dukelec/cdbus/hdl/cd_tx_bytes.v

/*
 * This Source Code Form is subject to the terms of the CERN Open
 * Hardware Licence Version 2 - Strongly Reciprocal (CERN-OHL-S v2):
 * https://ohwr.org/cern_ohl_s_v2.txt (see the LICENSE file).
 * Notice: The CDBUS Exception (see the LICENSE_EXCEPTION file)
 * grants free commercial use in FPGAs and other programmable logic
 * devices; it does not extend to ASIC design or manufacturing.
 *
 * Copyright (c) 2017-2026 DUKELEC, All rights reserved.
 *
 * Author: Duke Fong <d@d-l.io>
 */

module cd_tx_bytes(
        input               clk,
        input               reset_n,

        input               user_crc,
        input               raw,        // transparent mode: skip the first 3 bytes
        input               abort,

        output reg  [7:0]   data,
        output              has_data,
        input               ack_data,
        output reg          is_crc_byte,
        output reg          is_last_byte,
        input       [15:0]  crc_data,

        input               ram_unread,
        input               ram_wr_en,
        input       [7:0]   ram_rd_byte,
        output      [7:0]   ram_rd_addr,
        output              ram_rd_en,
        output reg          ram_rd_done
    );

assign has_data = ram_unread && !ram_rd_done && hdr_done;
assign ram_rd_en = ram_unread;

reg [8:0] byte_cnt;
assign ram_rd_addr = byte_cnt[7:0];
reg [7:0] data_len; // backup 3rd byte
reg hdr_done;       // raw mode: header prefetched, 2 clocks per byte for ram latency
reg pf_tick;


always @(posedge clk)
    if (!ram_unread || ram_rd_done) begin
        byte_cnt <= 0;
        data_len <= 0;
        hdr_done <= !raw;
        pf_tick <= 0;
        is_crc_byte <= 0;
        is_last_byte <= 0;
    end
    else begin
        data <= ram_rd_byte;
        pf_tick <= !pf_tick && !ram_wr_en; // read lost to write in single port ram

        if (byte_cnt == 2) begin
            data_len <= ram_rd_byte;
            if (pf_tick)
                hdr_done <= 1;
        end

        // we have enough time to change the byte which send at second bit
        else if (byte_cnt == data_len + 3) begin
            if (!user_crc)
                data <= crc_data[7:0];
            is_crc_byte <= 1;
        end
        else if (byte_cnt == data_len + 4) begin
            if (!user_crc)
                data <= crc_data[15:8];
            is_last_byte <= 1;
        end

        if (ack_data || (pf_tick && !hdr_done))
            byte_cnt <= byte_cnt + 1'd1;
    end


always @(posedge clk) begin
    ram_rd_done <= 0;
    if (abort || (is_last_byte && ack_data))
        ram_rd_done <= 1;
end

endmodule
