dukelec/cdbus/tests/cdbus_wrapper_dft.v

/*
 * This Source Code Form is subject to the terms of the CERN Open
 * Hardware Licence Version 2 - Strongly Reciprocal (CERN-OHL-S v2):
 * https://ohwr.org/cern_ohl_s_v2.txt (see the LICENSE file).
 * Notice: The CDBUS Exception (see the LICENSE_EXCEPTION file)
 * grants free commercial use in FPGAs and other programmable logic
 * devices; it does not extend to ASIC design or manufacturing.
 *
 * Copyright (c) 2017-2026 DUKELEC, All rights reserved.
 *
 * Author: Duke Fong <d@d-l.io>
 */

`timescale 1 ns / 1 ps
`define CD_CHIP_SELECT

module cdbus_wrapper_dft(
        input       clk0,
        input       clk1,
        input       clk2,
        input       reset0,
        input       reset1,
        input       reset2,
        input       cs0,
        input       cs1,
        input       cs2,

        input       [4:0] csr_addr0,
        input       csr_read0,
        output      [7:0] csr_rdata0,
        input       csr_write0,
        input       [7:0] csr_wdata0,

        input       [4:0] csr_addr1,
        input       csr_read1,
        output      [7:0] csr_rdata1,
        input       csr_write1,
        input       [7:0] csr_wdata1,

        input       [4:0] csr_addr2,
        input       csr_read2,
        output      [7:0] csr_rdata2,
        input       csr_write2,
        input       [7:0] csr_wdata2,

        output      irq0,
        output      irq1,
        output      irq2,

        inout       bus_a,

        input       dbg0,
        input       dbg1
    );

wire tx0;
wire tx1;
wire tx2;
wire tx_en0;
wire tx_en1;
wire tx_en2;

wire rx0 = tx_en0 === 1 ? tx0 : (bus_a === 1'bx ? 1'bx : (bus_a !== 0));
wire rx1 = tx_en1 === 1 ? tx1 : (bus_a === 1'bx ? 1'bx : (bus_a !== 0));
wire rx2 = tx_en2 === 1 ? tx2 : (bus_a === 1'bx ? 1'bx : (bus_a !== 0));

wire b0_is0 = tx_en0 === 1 && tx0 === 0;
wire b1_is0 = tx_en1 === 1 && tx1 === 0;
wire b2_is0 = tx_en2 === 1 && tx2 === 0;
wire b0_is1 = tx_en0 === 1 && tx0 === 1;
wire b1_is1 = tx_en1 === 1 && tx1 === 1;
wire b2_is1 = tx_en2 === 1 && tx2 === 1;

wire [2:0] is0_cnt = b0_is0 + b1_is0 + b2_is0;
wire [2:0] is1_cnt = b0_is1 + b1_is1 + b2_is1;

reg bus_reg;
assign bus_a = bus_reg;

always @(*)
    if (is0_cnt == 0 && is1_cnt != 0)
        bus_reg = 1;
    else if (is0_cnt != 0 && is1_cnt == 0)
        bus_reg = 0;
    else if (is0_cnt == 0 && is1_cnt == 0)
        bus_reg = 1'bz;
    else
        bus_reg = 1'bx;


cdbus cdbus_m0(
          .clk(clk0),
          .reset_n(reset0),
          .chip_select(cs0),
          .irq(irq0),
          
          .csr_address(csr_addr0),
          .csr_read(csr_read0),
          .csr_readdata(csr_rdata0),
          .csr_write(csr_write0),
          .csr_writedata(csr_wdata0),
          
          .rx(rx0),
          .tx(tx0),
          .tx_en(tx_en0)
      );

cdbus cdbus_m1(
          .clk(clk1),
          .reset_n(reset1),
          .chip_select(cs1),
          .irq(irq1),
          
          .csr_address(csr_addr1),
          .csr_read(csr_read1),
          .csr_readdata(csr_rdata1),
          .csr_write(csr_write1),
          .csr_writedata(csr_wdata1),
          
          .rx(rx1),
          .tx(tx1),
          .tx_en(tx_en1)
      );

cdbus cdbus_m2(
          .clk(clk2),
          .reset_n(reset2),
          .chip_select(cs2),
          .irq(irq2),
          
          .csr_address(csr_addr2),
          .csr_read(csr_read2),
          .csr_readdata(csr_rdata2),
          .csr_write(csr_write2),
          .csr_writedata(csr_wdata2),
          
          .rx(rx2),
          .tx(tx2),
          .tx_en(tx_en2)
      );

initial begin
    $dumpfile("cdbus.vcd");
    $dumpvars();
end

endmodule
