dukelec/cdbus/tests/common.py

# This Source Code Form is subject to the terms of the CERN Open
# Hardware Licence Version 2 - Strongly Reciprocal (CERN-OHL-S v2):
# https://ohwr.org/cern_ohl_s_v2.txt (see the LICENSE file).
# Notice: The CDBUS Exception (see the LICENSE_EXCEPTION file)
# grants free commercial use in FPGAs and other programmable logic
# devices; it does not extend to ASIC design or manufacturing.
#
# Copyright (c) 2017-2026 DUKELEC, All rights reserved.
#
# Author: Duke Fong <d@d-l.io>
#

import cocotb
from cocotb.types import Logic, LogicArray
from cocotb.triggers import RisingEdge, FallingEdge, ReadOnly, Timer
from cocotb.clock import Clock

# pip3 install pythoncrc
from PyCRC.CRC16 import CRC16

def modbus_crc(data):
    return CRC16(modbus_flag=True).calculate(data).to_bytes(2, byteorder='little')

IS_32BITS           = False
DFT_VERSION         = 0x0f

REG_VERSION         = 0x00
REG_SETTING         = 0x02
REG_PIN_CFG         = 0x03
REG_IDLE_WAIT_LEN   = 0x04
REG_TX_PERMIT_LEN_L = 0x05
REG_TX_PERMIT_LEN_H = 0x06
REG_MAX_IDLE_LEN_L  = 0x07
REG_MAX_IDLE_LEN_H  = 0x08
REG_TX_PRE_LEN      = 0x09
REG_FILTER          = 0x0b
REG_DIV_LS_L        = 0x0c
REG_DIV_LS_H        = 0x0d
REG_DIV_HS_L        = 0x0e
REG_DIV_HS_H        = 0x0f
REG_INT_MASK_L      = 0x10
REG_INT_MASK_H      = 0x11
REG_INT_FLAG_L      = 0x12
REG_INT_FLAG_H      = 0x13
REG_RX_LEN          = 0x14
REG_DAT             = 0x15
REG_CTRL            = 0x16
REG_DAT_HOLD        = 0x17
REG_RX_ADDR         = 0x18
REG_FILTER_M0       = 0x1a
REG_FILTER_M1       = 0x1b
REG_FILTER_MSK0     = 0x1c
REG_FILTER_MSK1     = 0x1d

BIT_SETTING_NO_DROP         = 1 << 5
BIT_SETTING_USER_CRC        = 1 << 4
BIT_SETTING_RAW_LOOPBACK    = 1 << 3
BIT_SETTING_RAW             = 1 << 2
BIT_SETTING_MODE_HALF       = 0 << 0
BIT_SETTING_MODE_ARBIT      = 1 << 0
BIT_SETTING_MODE_BS         = 2 << 0
BIT_SETTING_MODE_FULL       = 3 << 0

BIT_PIN_CFG_RX_INVERT       = 1 << 3
BIT_PIN_CFG_TX_INVERT       = 1 << 2
BIT_PIN_CFG_TX_KEEP_LOW     = 1 << 1
BIT_PIN_CFG_TX_PUSH_PULL    = 1 << 0

BIT_FLAG_TX_ERROR           = 1 << 7
BIT_FLAG_TX_CD              = 1 << 6
BIT_FLAG_TX_BUF_CLEAN       = 1 << 5
BIT_FLAG_TX_BUF_FREE        = 1 << 4
BIT_FLAG_RX_ERROR           = 1 << 3
BIT_FLAG_RX_LOST            = 1 << 2
BIT_FLAG_RX_BREAK           = 1 << 1
BIT_FLAG_RX_PENDING         = 1 << 0

BIT_RX_RST                  = 1 << 7
BIT_RX_CLR_PENDING          = 1 << 4
BIT_TX_ABORT                = 1 << 3
BIT_TX_DROP                 = 1 << 2
BIT_TX_SEND_BREAK           = 1 << 1
BIT_TX_START                = 1 << 0


async def _send_bytes(dut, bytes_, sys_clk, factor, is_z=True):
    clk_period = 1000000000000 / sys_clk
    await Timer(1000)
    factor += 1
    for byte in bytes_:
        dut.bus_a.value = 0
        await Timer(factor * clk_period)
        for i in range(0, 8):
            if byte & 0x01 == 0:
                dut.bus_a.value = 0
            else:
                dut.bus_a.value = Logic('z') if is_z else 1
            await Timer(factor * clk_period)
            byte = byte >> 1
        dut.bus_a.value = Logic('z') if is_z else 1
        await Timer(factor * clk_period)
        dut.bus_a.value = Logic('z')

# Pass in a frame of data from the outside of the dut.
async def send_frame(dut, bytes_, sys_clk, factor_l, factor_h):
    await _send_bytes(dut, bytes_[0:1], sys_clk, factor_l)
    await _send_bytes(dut, bytes_[1:], sys_clk, factor_h, False)
    await _send_bytes(dut, modbus_crc(bytes_), sys_clk, factor_h, False)


async def reset(dut, idx, duration=10000):
    dut._log.debug(f'idx{idx}: resetting')
    getattr(dut, f'reset{idx}').value = 0
    await Timer(duration)
    await RisingEdge(getattr(dut, f'clk{idx}'))
    getattr(dut, f'reset{idx}').value = 1
    dut._log.debug(f'idx{idx}: out of reset')
    getattr(dut, f'cs{idx}').value = 0

# the read is taken at the clock edge, the data is valid in the clock after it
# (csr_address is kept until then); a burst takes one byte per clock
async def csr_read(dut, idx, address, len_=1):
    await RisingEdge(getattr(dut, f'clk{idx}'))
    getattr(dut, f'cs{idx}').value = 1
    getattr(dut, f'csr_addr{idx}').value = address
    getattr(dut, f'csr_read{idx}').value = 1
    ret = []
    for i in range(len_):
        await RisingEdge(getattr(dut, f'clk{idx}'))
        if i == len_ - 1:
            getattr(dut, f'csr_read{idx}').value = 0
            getattr(dut, f'cs{idx}').value = 0
        await ReadOnly()
        ret.append(getattr(dut, f'csr_rdata{idx}').value)
    await RisingEdge(getattr(dut, f'clk{idx}')) # leave the read-only phase
    return ret if len_ > 1 else ret[0]

async def csr_write(dut, idx, address, data, burst=False):
    addr_len = len(getattr(dut, f'csr_addr{idx}'))
    wdata_len = len(getattr(dut, f'csr_wdata{idx}'))
    
    await RisingEdge(getattr(dut, f'clk{idx}'))
    getattr(dut, f'cs{idx}').value = 1
    getattr(dut, f'csr_addr{idx}').value = address
    getattr(dut, f'csr_wdata{idx}').value = data
    getattr(dut, f'csr_write{idx}').value = 1
    if not burst:
        await RisingEdge(getattr(dut, f'clk{idx}'))
        getattr(dut, f'csr_write{idx}').value = 0
        getattr(dut, f'csr_addr{idx}').value = LogicArray('x' * addr_len)
        getattr(dut, f'csr_wdata{idx}').value = LogicArray('x' * wdata_len)
        getattr(dut, f'cs{idx}').value = 0


async def check_version(dut, idx):
    value = await csr_read(dut, idx, REG_VERSION)
    dut._log.info(f'idx{idx}: REG_VERSION: 0x%02x' % int(value))
    if value != DFT_VERSION:
        dut._log.error(f'idx{idx}: version mismatch')
        exit(-1)

async def set_div(dut, idx, div_ls, div_hs):
    await csr_write(dut, idx, REG_DIV_LS_H, div_ls >> 8, True)
    await csr_write(dut, idx, REG_DIV_LS_L, div_ls & 0xff, True)
    await csr_write(dut, idx, REG_DIV_HS_H, div_hs >> 8, True)
    await csr_write(dut, idx, REG_DIV_HS_L, div_hs & 0xff, False)

async def set_max_idle_len(dut, idx, max_idle_len):
    await csr_write(dut, idx, REG_MAX_IDLE_LEN_H, max_idle_len >> 8, True)
    await csr_write(dut, idx, REG_MAX_IDLE_LEN_L, max_idle_len & 0xff, False)

async def set_tx_permit_len(dut, idx, tx_permit_len):
    await csr_write(dut, idx, REG_TX_PERMIT_LEN_H, tx_permit_len >> 8, True)
    await csr_write(dut, idx, REG_TX_PERMIT_LEN_L, tx_permit_len & 0xff, False)

async def write_tx(dut, idx, bytes_, reg=REG_DAT):
    if len(bytes_) == 0:
        return
    for i in range(len(bytes_)):
        await csr_write(dut, idx, reg, bytes_[i], i < len(bytes_) - 1)
    await RisingEdge(getattr(dut, f'clk{idx}')) # let the auto submit finish before the next transfer

async def seek_rx(dut, idx, offset): # byte offset
    await csr_write(dut, idx, REG_RX_ADDR, offset)

async def read_rx(dut, idx, len_, reg=REG_DAT):
    if len_ == 0:
        return b''
    vals = await csr_read(dut, idx, reg, len_)
    return bytes([int(v) for v in (vals if len_ > 1 else [vals])])

async def read_rx_len(dut, idx):
    return await csr_read(dut, idx, REG_RX_LEN)

async def read_int_flag(dut, idx):
    return await csr_read(dut, idx, REG_INT_FLAG_L)

async def read_int_flag3(dut, idx):
    return await csr_read(dut, idx, REG_INT_FLAG_L, 3)


async def exit_err():
    await Timer(1000, unit='ns')
    exit(-1)

async def exit_ok():
    await Timer(10, unit='us')
    with open('.exit_ok', 'w') as f:
        f.write('ok')
