dukelec/cdbus/tests/test_bs_mode.py

# This Source Code Form is subject to the terms of the CERN Open
# Hardware Licence Version 2 - Strongly Reciprocal (CERN-OHL-S v2):
# https://ohwr.org/cern_ohl_s_v2.txt (see the LICENSE file).
# Notice: The CDBUS Exception (see the LICENSE_EXCEPTION file)
# grants free commercial use in FPGAs and other programmable logic
# devices; it does not extend to ASIC design or manufacturing.
#
# Copyright (c) 2017-2026 DUKELEC, All rights reserved.
#
# Author: Duke Fong <d@d-l.io>
#

from common import *

@cocotb.test(timeout_time=500, timeout_unit='us')
async def test_cdbus(dut):
    dut._log.info('test_cdbus start.')
    
    sys_clk = 40000000
    clk_period = 1000000000000 / sys_clk

    cocotb.start_soon(Clock(dut.clk0, clk_period).start())
    cocotb.start_soon(Clock(dut.clk1, clk_period).start())
    cocotb.start_soon(Clock(dut.clk2, clk_period).start())
    await reset(dut, 0)
    await reset(dut, 1)
    await reset(dut, 2)
    await check_version(dut, 0)
    await check_version(dut, 1)
    await check_version(dut, 2)
    
    val = await csr_read(dut, 0, REG_SETTING)
    dut._log.info(f'idx0 REG_SETTING: 0x{int(val):02x}')

    await csr_write(dut, 0, REG_SETTING, 0b00000010) # bs mode
    await csr_write(dut, 1, REG_SETTING, 0b00000010)
    await csr_write(dut, 2, REG_SETTING, 0b00000010)
    await csr_write(dut, 0, REG_PIN_CFG, 0b00000001) # push-pull
    await csr_write(dut, 1, REG_PIN_CFG, 0b00000001)
    await csr_write(dut, 2, REG_PIN_CFG, 0b00000001)
    await csr_write(dut, 2, REG_INT_MASK_L, 0b11001101) # not select break rx
    
    await set_max_idle_len(dut, 0, 40)
    await set_max_idle_len(dut, 1, 40)
    await set_max_idle_len(dut, 2, 40)
    
    await set_tx_permit_len(dut, 0, 10)
    await set_tx_permit_len(dut, 1, 20)
    await set_tx_permit_len(dut, 2, 30)

    await set_div(dut, 0, 2, 2) # max speed
    await set_div(dut, 1, 2, 2)
    await set_div(dut, 2, 2, 2)
    
    await csr_write(dut, 0, REG_FILTER, 0x55)
    await csr_write(dut, 1, REG_FILTER, 0xa5)
    await csr_write(dut, 2, REG_FILTER, 0x03)
    
    
    await Timer(10, unit='us') # wait exceed max idle
    
    # start tx at same time
    cocotb.start_soon(write_tx(dut, 0, b'\x55\x03\x01\xc5')) # node 0x55 send to 0x03
    cocotb.start_soon(write_tx(dut, 1, b'\xa5\x03\x01\xca')) # node 0xa5 send to 0x03

    await RisingEdge(dut.irq2)
    val = await read_int_flag(dut, 2)
    dut._log.info(f'REG_INT_FLAG: 0x{int(val):02x}')
    if not (int(val) & BIT_FLAG_RX_BREAK):
        dut._log.error(f'idx2: not receive break')
        await exit_err()
    
    str_ = (await read_rx(dut, 2, 4)).hex() # read 4 bytes
    dut._log.info(f'idx2: received: {str_}')
    if str_ != '550301c5':
        dut._log.error(f'idx2: receive mismatch first frame')
        await exit_err()
    
    #await csr_write(dut, 2, REG_CTRL, BIT_RX_CLR_PENDING)
    await Timer(500, unit='ns')
    
    await RisingEdge(dut.irq2)
    val = await read_int_flag(dut, 2)
    dut._log.info(f'REG_INT_FLAG: 0x{int(val):02x}')
    
    str_ = (await read_rx(dut, 2, 4)).hex() # read 4 bytes
    dut._log.info(f'idx2: received: {str_}')
    if str_ != 'a50301ca':
        dut._log.error(f'idx2: receive mismatch second frame')
        await exit_err()
    
    #await csr_write(dut, 2, REG_CTRL, BIT_RX_CLR_PENDING)
    await FallingEdge(dut.irq2)
    
    
    await Timer(10, unit='us') # wait exceed max idle
    
    cocotb.start_soon(write_tx(dut, 1, b'\xa5\x03\x01\xca')) # node 0xa5 send to 0x03
    dut.dbg0.value = 0
    await Timer(2700, unit='ns') # wait frame pending after tx permit
    dut.dbg0.value = 1
    cocotb.start_soon(write_tx(dut, 0, b'\x55\x03\x01\xc5')) # node 0x55 send to 0x03
    
    await RisingEdge(dut.irq2)
    val = await read_int_flag(dut, 2)
    dut._log.info(f'REG_INT_FLAG: 0x{int(val):02x}')
    if not (int(val) & BIT_FLAG_RX_BREAK):
        dut._log.error(f'idx2: not receive break')
        await exit_err()
    
    str_ = (await read_rx(dut, 2, 4)).hex() # read 4 bytes
    dut._log.info(f'idx2: received: {str_}')
    if str_ != 'a50301ca':
        dut._log.error(f'idx2: receive mismatch first frame')
        await exit_err()
    
    #await csr_write(dut, 2, REG_CTRL, BIT_RX_CLR_PENDING)
    await Timer(500, unit='ns')
    
    await RisingEdge(dut.irq2)
    val = await read_int_flag(dut, 2)
    dut._log.info(f'REG_INT_FLAG: 0x{int(val):02x}')
    
    str_ = (await read_rx(dut, 2, 4)).hex() # read 4 bytes
    dut._log.info(f'idx2: received: {str_}')
    if str_ != '550301c5':
        dut._log.error(f'idx2: receive mismatch second frame')
        await exit_err()
    
    #await csr_write(dut, 2, REG_CTRL, BIT_RX_CLR_PENDING)
    await FallingEdge(dut.irq2)
    
    dut._log.info('test_cdbus done.')
    await exit_ok()
