dukelec/cdbus/example/pll/cdctl_pll.v

module cdctl_pll(REFERENCECLK,
                 PLLOUTCORE,
                 PLLOUTGLOBAL,
                 RESET,
                 LOCK);

input REFERENCECLK;
input RESET;    /* To initialize the simulation properly, the RESET signal (Active Low) must be asserted at the beginning of the simulation */ 
output PLLOUTCORE;
output PLLOUTGLOBAL;
output LOCK;

SB_PLL40_CORE cdctl_pll_inst(.REFERENCECLK(REFERENCECLK),
                             .PLLOUTCORE(PLLOUTCORE),
                             .PLLOUTGLOBAL(PLLOUTGLOBAL),
                             .EXTFEEDBACK(),
                             .DYNAMICDELAY(),
                             .RESETB(RESET),
                             .BYPASS(1'b0),
                             .LATCHINPUTVALUE(),
                             .LOCK(LOCK),
                             .SDI(),
                             .SDO(),
                             .SCLK());

//\\ Fin=16, Fout=40;
defparam cdctl_pll_inst.DIVR = 4'b0000;
defparam cdctl_pll_inst.DIVF = 7'b0100111;
defparam cdctl_pll_inst.DIVQ = 3'b100;
defparam cdctl_pll_inst.FILTER_RANGE = 3'b001;
defparam cdctl_pll_inst.FEEDBACK_PATH = "SIMPLE";
defparam cdctl_pll_inst.DELAY_ADJUSTMENT_MODE_FEEDBACK = "FIXED";
defparam cdctl_pll_inst.FDA_FEEDBACK = 4'b0000;
defparam cdctl_pll_inst.DELAY_ADJUSTMENT_MODE_RELATIVE = "FIXED";
defparam cdctl_pll_inst.FDA_RELATIVE = 4'b0000;
defparam cdctl_pll_inst.SHIFTREG_DIV_MODE = 2'b00;
defparam cdctl_pll_inst.PLLOUT_SELECT = "GENCLK";
defparam cdctl_pll_inst.ENABLE_ICEGATE = 1'b0;

endmodule
